Colin-J-Smith/CLADE/camera_init.py

# camera_init.py
# Author: Lea Chandler
# Date: 2/17/2020
# 
# Camera pipeline object initialization for the Luxonis USB3 stereo camera
# using the DepthAI shared library. Code modified from:
# https://github.com/luxonis/depthai-python-extras

# --------------------------
# IMPORTS
# --------------------------

import luxonis_resources.depthai as depthai
from luxonis_resources import utils

import os
import json
from os import path
from pathlib import Path


# --------------------------
# RESOURCE PATHS
# --------------------------

def relative_to_abs_path(relative_path):
    dirname = Path(__file__).parent
    return str((dirname / relative_path).resolve())

device_cmd_file    = relative_to_abs_path('luxonis_resources/depthai.cmd')
blob_file          = relative_to_abs_path('luxonis_resources/mobilenet_ssd.blob')

# --------------------------
# INIT
# --------------------------

def camera_init():
    calc_dist_to_bb = False
    streams = json.loads('{"streams": [{"name": "previewout", "max_fps": 12.0}]}')

    default_config = {
        'streams': ['previewout'],
        'depth': {
            'calibration_file': '',
            'padding_factor': 0.3
        },
        'ai': { 
            'blob_file': blob_file,
            'calc_dist_to_bb': calc_dist_to_bb
        },
        'board_config': {
            'swap_left_and_right_cameras': True,    # True for 1097 (RPi Compute) and 1098OBC (USB w/onboard cameras)
            'left_fov_deg': 69.0,                   # Same on 1097 and 1098OBC
            'left_to_right_distance_cm': 7.5,       # Distance between stereo cameras
        }
    }
    config = utils.merge(streams, default_config)

    # camera init
    if not depthai.init_device(device_cmd_file):
        print("Error initializing device. Try to reset it.")
        exit(1)

    # create the pipeline, here is the first connection with the device
    pipeline = depthai.create_pipeline(config=config)
    if pipeline is None:
        print('Pipeline is not created.')
        exit(2)

    return pipeline
